Makers-Oakland-University/laser-tanks/Image Recognition/ABS-or-PLA Big.jpg

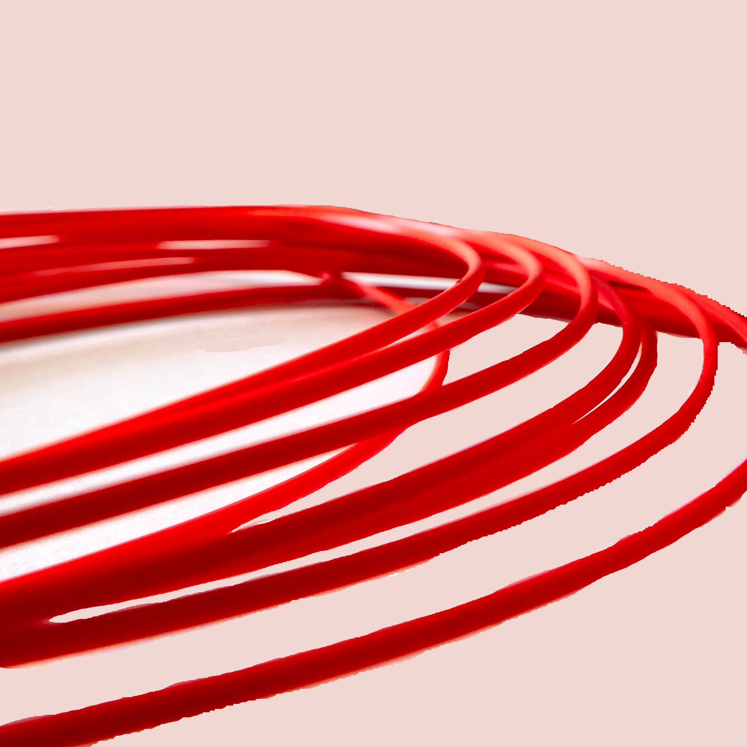
Image Recognition/ABS-or-PLA Big.jpg
