Makers-Oakland-University/laser-tanks/Image Recognition/Test Image Group/input/1.PNG

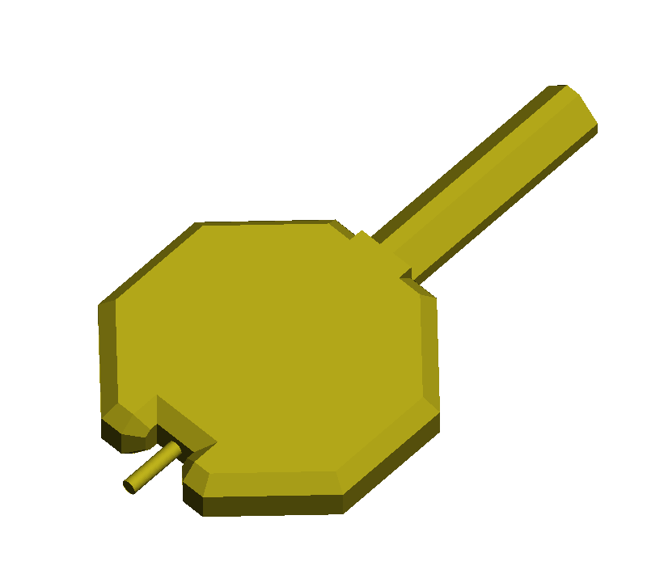
Image Recognition/Test Image Group/input/1.PNG
