Makers-Oakland-University/laser-tanks/Image Recognition/Test Image Group/input/2.PNG

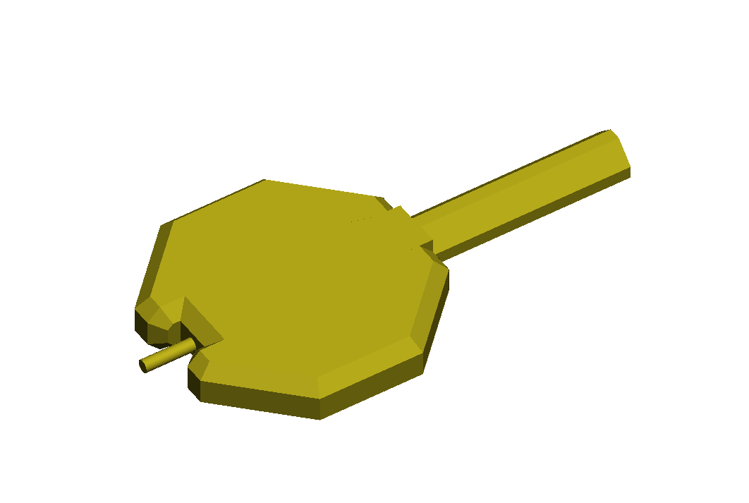
Image Recognition/Test Image Group/input/2.PNG
