Makers-Oakland-University/laser-tanks/Image Recognition/Test Image Group/input/3.PNG

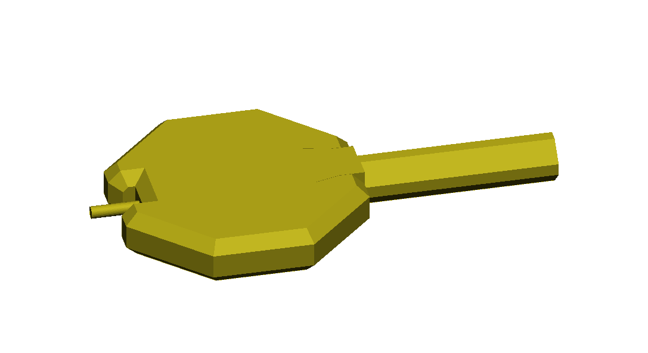
Image Recognition/Test Image Group/input/3.PNG
