Makers-Oakland-University/laser-tanks/Image Recognition/Test Image Group/input/4.PNG

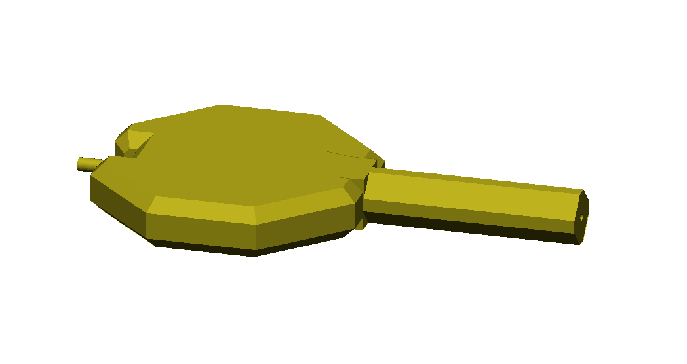
Image Recognition/Test Image Group/input/4.PNG
