Makers-Oakland-University/laser-tanks/Image Recognition/Test Image Group/input/5.PNG

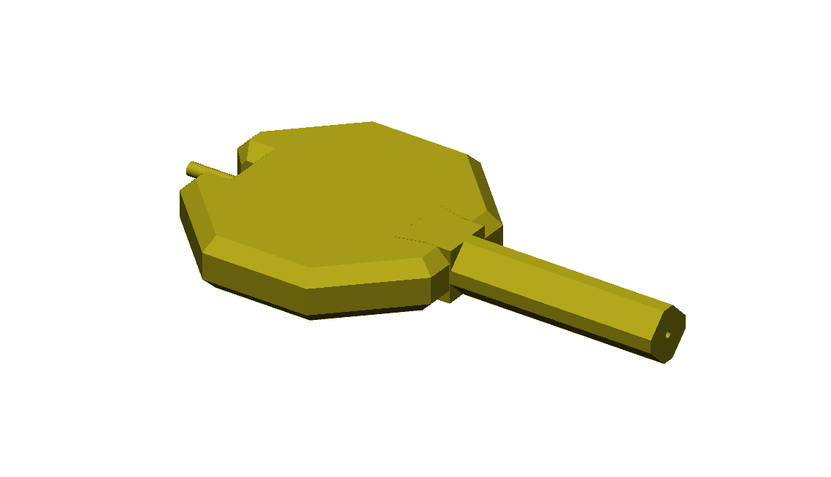
Image Recognition/Test Image Group/input/5.PNG
