Makers-Oakland-University/laser-tanks/Image Recognition/Test Image Group/input/6.PNG

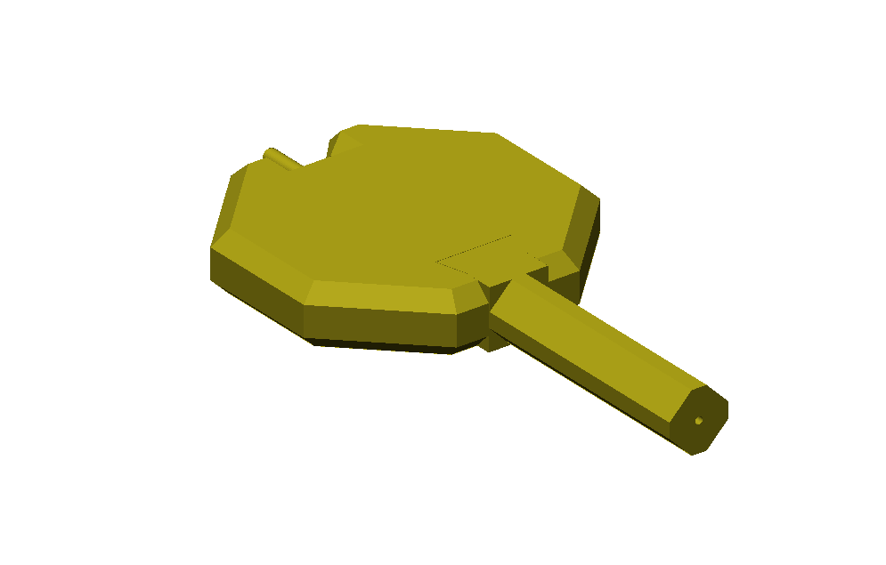
Image Recognition/Test Image Group/input/6.PNG
