Makers-Oakland-University/laser-tanks/Image Recognition/Test Image Group/input/7.PNG

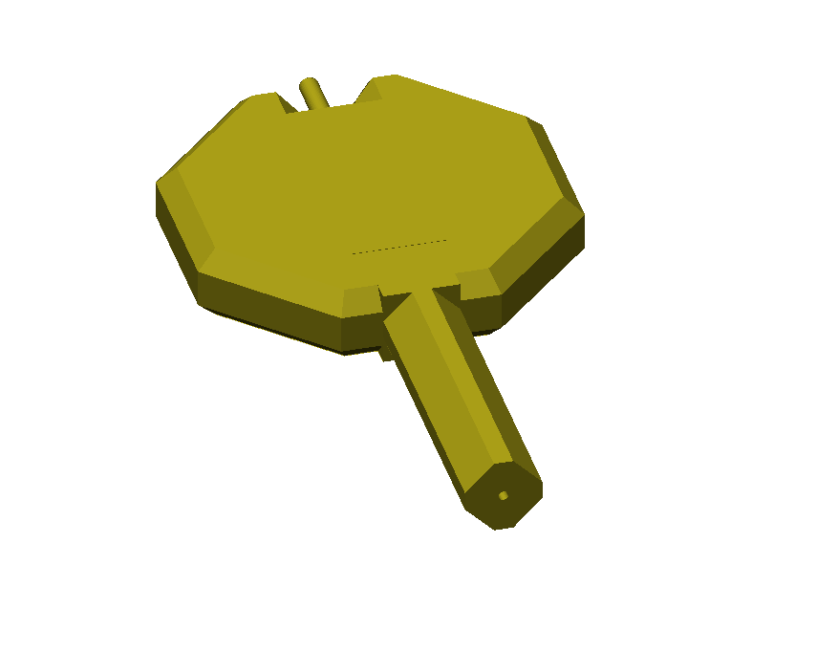
Image Recognition/Test Image Group/input/7.PNG
