Makers-Oakland-University/laser-tanks/Image Recognition/Test Image Group/input/8.PNG

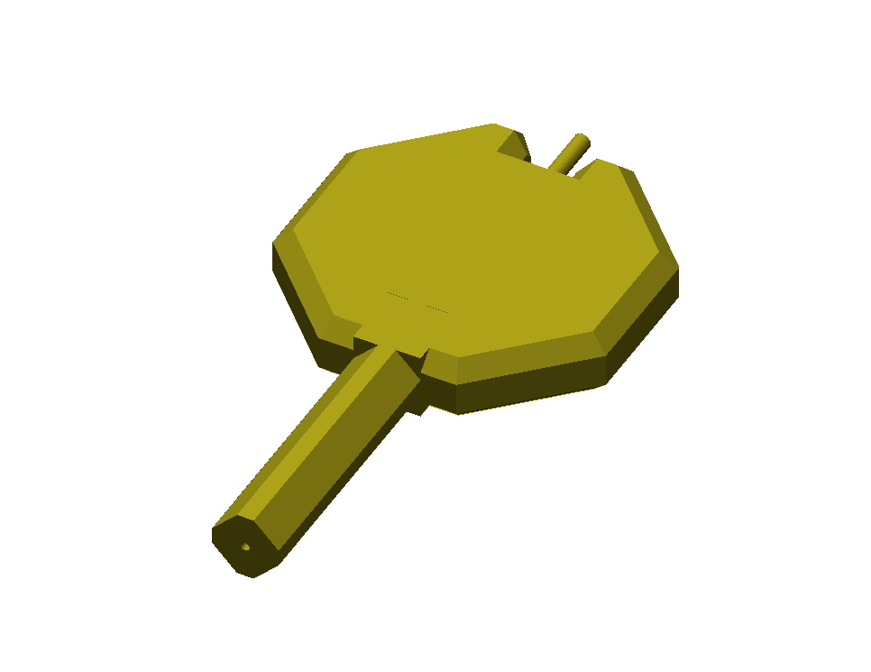
Image Recognition/Test Image Group/input/8.PNG
