Makers-Oakland-University/laser-tanks/Image Recognition/Test Image Group/input/9.PNG

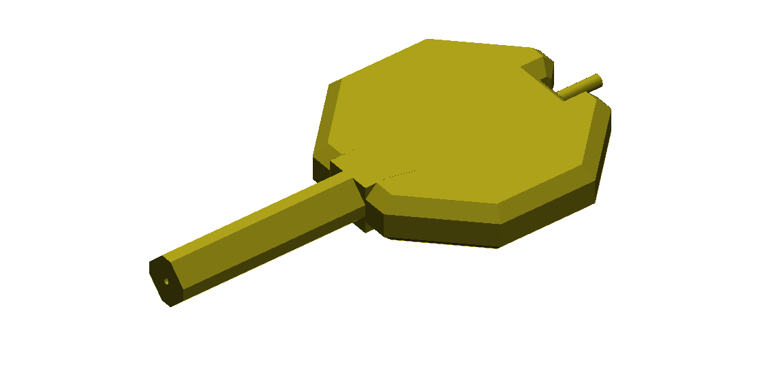
Image Recognition/Test Image Group/input/9.PNG
