Makers-Oakland-University/laser-tanks/Image Recognition/Test Image Group/input/10.PNG

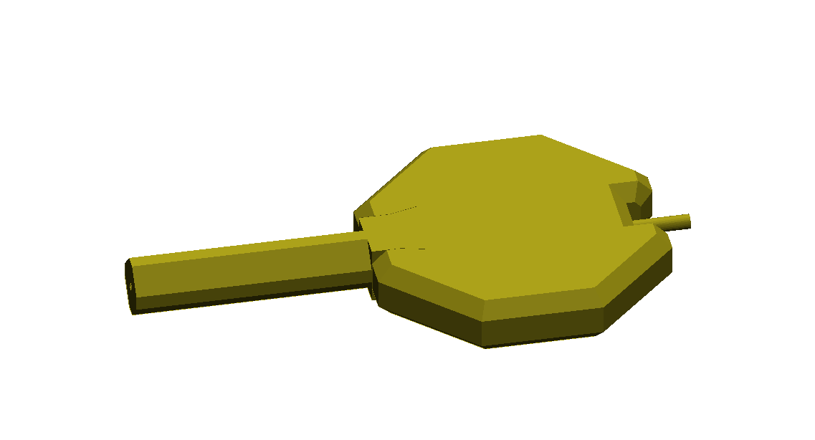
Image Recognition/Test Image Group/input/10.PNG
