Makers-Oakland-University/laser-tanks/Image Recognition/Test Image Group/input/11.PNG

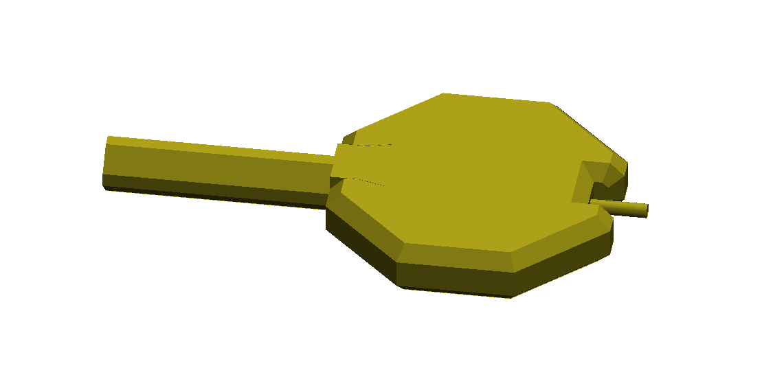
Image Recognition/Test Image Group/input/11.PNG
