Makers-Oakland-University/laser-tanks/Image Recognition/Test Image Group/input/12.PNG

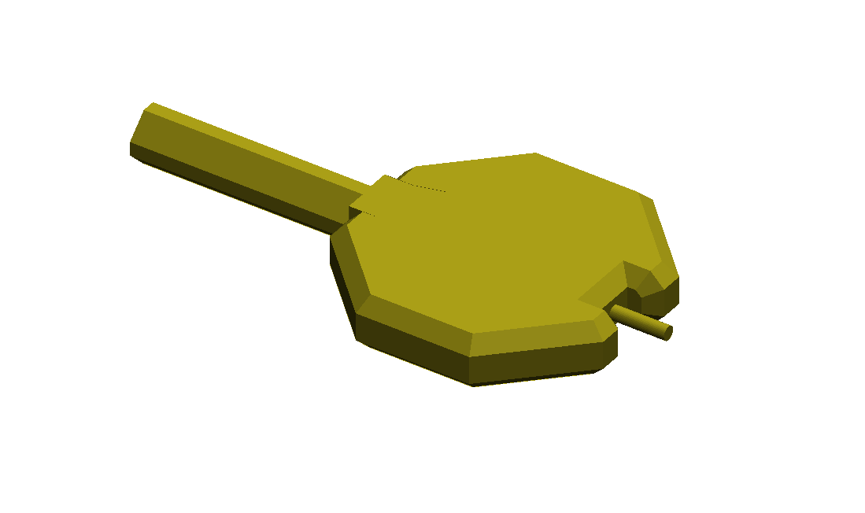
Image Recognition/Test Image Group/input/12.PNG
