Makers-Oakland-University/laser-tanks/Image Recognition/Test Image Group/input/13.PNG

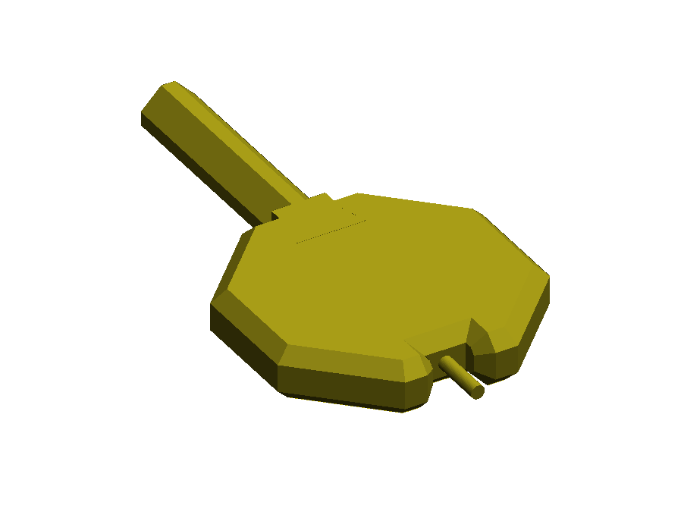
Image Recognition/Test Image Group/input/13.PNG
