Makers-Oakland-University/laser-tanks/Image Recognition/Test Image Group/input/side view.PNG

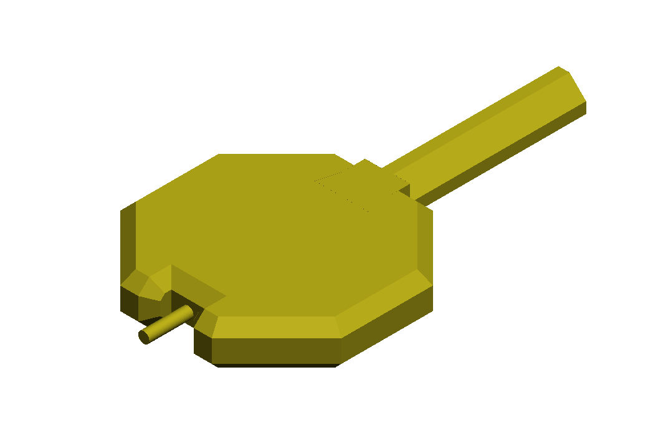
Image Recognition/Test Image Group/input/side view.PNG
