Makers-Oakland-University/laser-tanks/laser_tanks_r2/laser_tanks_r2/laser_tanks_r2.sch

## KiCad design laser_tanks_r2/laser_tanks_r2/laser_tanks_r2.sch (2020-03-07)

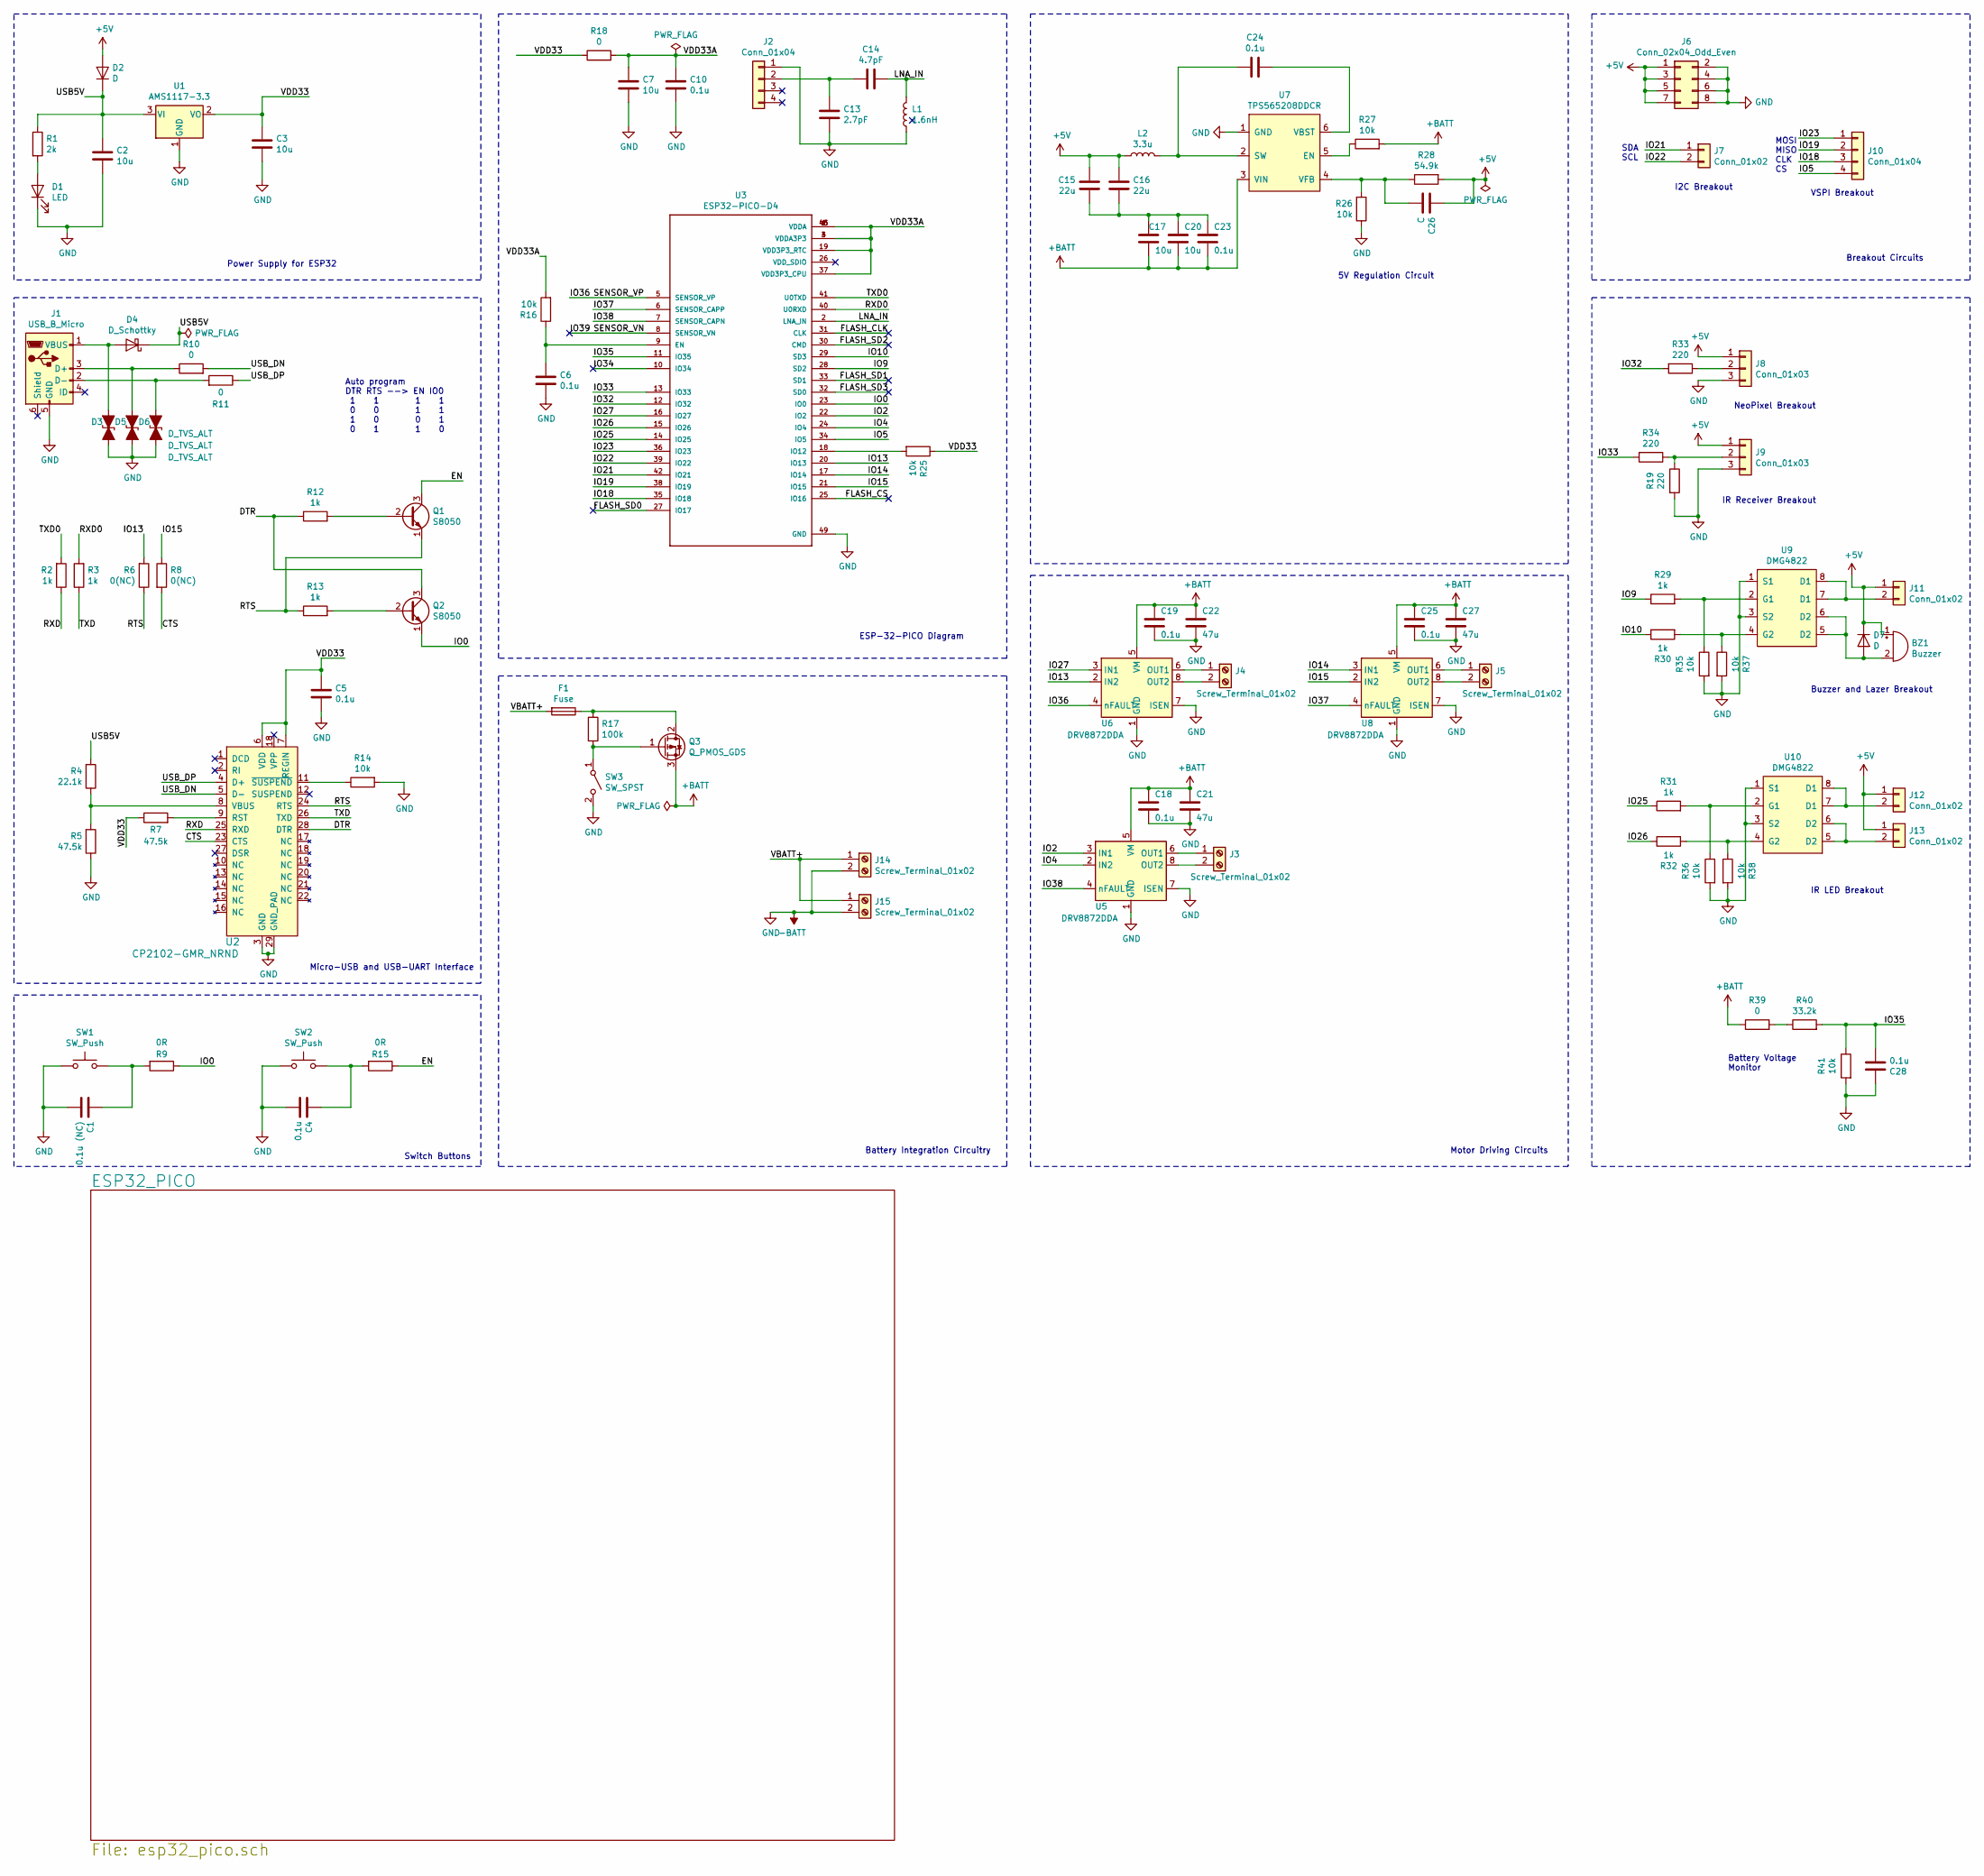
[picture p21: schematic laser_tanks_r2.sch]

Parts:
BZ1: Buzzer; Piezo_Transducer_THT_PS1240P02BT
C1: 0.1u (NC); C_0603_1608Metric_Pad1.05x0.95mm_HandSolder
C2, C3, C7, C17, C20: 10u; C_0805_2012Metric_Pad1.15x1.40mm_HandSolder
C4, C5, C6, C10, C18, C19, C23, C24, C25, C28: 0.1u; C_0603_1608Metric_Pad1.05x0.95mm_HandSolder
C13: 2.7pF; C_0603_1608Metric_Pad1.05x0.95mm_HandSolder
C14: 4.7pF; C_0603_1608Metric_Pad1.05x0.95mm_HandSolder
C15, C16: 22u; C_1206_3216Metric_Pad1.42x1.75mm_HandSolder
C21, C22, C27: 47u; CP_Elec_6.3x5.4
C26: C; C_0805_2012Metric_Pad1.15x1.40mm_HandSolder
D1: LED
D2, D7: D
D3, D5, D6: D_TVS_ALT
D4: D_Schottky
F1: Fuse
J1: USB_B_Micro
J2, J10: Conn_01x04
J3, J4, J5, J14, J15: Screw_Terminal_01x02
J6: Conn_02x04_Odd_Even
J7, J11, J12, J13: Conn_01x02
J8, J9: Conn_01x03
L1: 1.6nH
L2: 3.3u
Q1, Q2: S8050; TO-92_Inline
Q3: Q_PMOS_GDS
R1: 2k
R2, R3, R12, R13, R29, R30, R31, R32: 1k
R4: 22.1k
R5, R7: 47.5k
R6, R8: 0(NC)
R9, R15: 0R
R10, R11, R18, R39: 0
R14, R16, R25, R26, R27, R35, R36, R37, R38, R41: 10k
R17: 100k
R19, R33, R34: 220
R28: 54.9k
R40: 33.2k
SW1, SW2: SW_Push
SW3: SW_SPST
U1: AMS1117-3.3; SOT-223-3_TabPin2
U2: CP2102-GMR_NRND; VFQFN-28-1EP_5x5mm; MPN CP2102-GMR; Digi-Key_PN 336-1160-1-ND
U3: ESP32-PICO-D4; PQFN50P700X700X104-49N
U5, U6, U8: DRV8872DDA; Texas_HTSOP-8-1EP_3.9x4.9mm_P1.27mm_EP2.95x4.9mm_Mask2.4x3.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
U7: TPS565208DDCR
U9, U10: DMG4822

Connections:
+5V: BZ1.1 (-), C15.2, C16.2, C26.1, D2.2 (A), D7.1 (K), J6.1, J6.3, J6.5, J6.7, J8.1, J9.1, J11.1, J12.1, J13.1, L2.1, R28.2
+BATT: C17.1, C18.1, C19.1, C20.2, C21.1, C22.1, C23.2, C25.1, C27.1, Q3.3 (S), R27.2, R39.1, U5.5 (VM), U6.5 (VM), U7.3 (VIN), U8.5 (VM)
-BATT: C1.2, C2.2, C3.2, C4.2, C5.2, C6.2, C7.2, C10.2, C13.2, C18.2, C19.2, C21.2, C22.2, C25.2, C27.2, C28.1, D1.1 (K), D3.2 (A2), D5.2 (A2), D6.2 (A2), J1.5 (GND), J2.1, J6.2, J6.4, J6.6, J6.8, J8.3, J9.3, J14.2, J15.2, L1.1, R5.1, R14.2, R19.2, R26.1, R35.2, R36.2, R37.2, R38.2, R41.2, SW1.1, SW2.1, SW3.2 (B), U1.1 (GND), U2.3 (GND), U2.29 (GND_PAD), U3.49 (GND), U5.1 (GND), U5.7 (ISEN), U5.9 (GND), U6.1 (GND), U6.7 (ISEN), U6.9 (GND), U7.1 (GND), U8.1 (GND), U8.7 (ISEN), U8.9 (GND), U9.1 (S1), U9.3 (S2), U10.1 (S1), U10.3 (S2)
CTS: R8.2, U2.23 (CTS)
DTR: Q2.3 (C), R12.1, U2.28 (DTR)
EN: Q1.3 (C), R15.1
FLASH_CLK: U3.31 (CLK)
FLASH_CS: U3.25 (IO16)
FLASH_SD0: U3.27 (IO17)
FLASH_SD1: U3.33 (SD1)
FLASH_SD2: U3.30 (CMD)
FLASH_SD3: U3.32 (SD0)
IO0: Q2.1 (E), R9.1, U3.23 (IO0)
IO2: U3.22 (IO2), U5.3 (IN1)
IO4: U3.24 (IO4), U5.2 (IN2)
IO5: J10.4, U3.34 (IO5)
IO9: R29.1, U3.28 (SD2)
IO10: R30.1, U3.29 (SD3)
IO13: R6.2, U3.20 (IO13), U6.2 (IN2)
IO14: U3.17 (IO14), U8.3 (IN1)
IO15: R8.1, U3.21 (IO15), U8.2 (IN2)
IO18: J10.3, U3.35 (IO18)
IO19: J10.2, U3.38 (IO19)
IO21: J7.1, U3.42 (IO21)
IO22: J7.2, U3.39 (IO22)
IO23: J10.1, U3.36 (IO23)
IO25: R31.1, U3.14 (IO25)
IO26: R32.1, U3.15 (IO26)
IO27: U3.16 (IO27), U6.3 (IN1)
IO32: R33.2, U3.12 (IO32)
IO33: R34.2, U3.13 (IO33)
IO34: U3.10 (IO34)
IO35: C28.2, R40.2, R41.1, U3.11 (IO35)
IO36: U3.5 (SENSOR_VP), U6.4 (nFAULT)
IO37: U3.6 (SENSOR_CAPP), U8.4 (nFAULT)
IO38: U3.7 (SENSOR_CAPN), U5.4 (nFAULT)
IO39: U3.8 (SENSOR_VN)
LNA_IN: C14.1, L1.2, U3.2 (LNA_IN)
unnamed: BZ1.2 (+), D7.2 (A), U9.5 (D2), U9.6 (D2)
unnamed: C1.1, R9.2, SW1.2
unnamed: C4.1, R15.2, SW2.2
unnamed: C6.1, R16.1, U3.9 (EN)
unnamed: C13.1, C14.2, J2.2
unnamed: C15.1, C16.1, C17.2, C20.1, C23.1
unnamed: C24.1, U7.6 (VBST)
unnamed: C24.2, L2.2, U7.2 (SW)
unnamed: C26.2, R26.2, R28.1, U7.4 (VFB)
unnamed: D1.2 (A), R1.2
unnamed: D3.1 (A1), D4.2 (A), J1.1 (VBUS)
unnamed: D5.1 (A1), J1.3 (D+), R10.1
unnamed: D6.1 (A1), J1.2 (D-), R11.2
unnamed: F1.1, Q3.2 (D), R17.1
unnamed: J3.1, U5.6 (OUT1)
unnamed: J3.2, U5.8 (OUT2)
unnamed: J4.1, U6.6 (OUT1)
unnamed: J4.2, U6.8 (OUT2)
unnamed: J5.1, U8.6 (OUT1)
unnamed: J5.2, U8.8 (OUT2)
unnamed: J8.2, R33.1
unnamed: J9.2, R19.1, R34.1
unnamed: J11.2, U9.7 (D1), U9.8 (D1)
unnamed: J12.2, U10.7 (D1), U10.8 (D1)
unnamed: J13.2, U10.5 (D2), U10.6 (D2)
unnamed: Q1.2 (B), R12.2
unnamed: Q2.2 (B), R13.2
unnamed: Q3.1 (G), R17.2, SW3.1 (A)
unnamed: R4.1, R5.2, U2.8 (VBUS)
unnamed: R7.2, U2.9 (RST)
unnamed: R14.1, U2.11 (~SUSPEND)
unnamed: R25.2, U3.18 (IO12)
unnamed: R27.1, U7.5 (EN)
unnamed: R29.2, R35.1, U9.2 (G1)
unnamed: R30.2, R37.1, U9.4 (G2)
unnamed: R31.2, R36.1, U10.2 (G1)
unnamed: R32.2, R38.1, U10.4 (G2)
unnamed: R39.2, R40.1
RTS: Q1.1 (E), R6.1, R13.1, U2.24 (RTS)
RXD: R2.1, U2.25 (RXD)
RXD0: R3.2, U3.40 (U0RXD)
TXD: R3.1, U2.26 (TXD)
TXD0: R2.2, U3.41 (U0TXD)
USB5V: C2.1, D2.1 (K), D4.1 (K), R1.1, R4.2, U1.3 (VI)
USB_DN: R10.2, U2.5 (D-)
USB_DP: R11.1, U2.4 (D+)
VBATT+: F1.2, J14.1, J15.1
VDD33: C3.1, C5.1, R7.1, R18.1, R25.1, U1.2 (VO), U2.6 (VDD), U2.7 (REGIN)
VDD33A: C7.1, C10.1, R16.2, R18.2, U3.1 (VDDA), U3.3 (VDDA3P3), U3.4 (VDDA3P3), U3.19 (VDD3P3_RTC), U3.37 (VDD3P3_CPU), U3.43 (VDDA), U3.46 (VDDA)

Notes on the sheet:
Power Supply for ESP32
Auto program DTR RTS --> EN IO0 1 1 1 1 0 0 1 1 1 0 0 1 0 1 1 0
Micro-USB and USB-UART Interface
Switch Buttons
ESP-32-PICO Diagram
5V Regulation Circuit
VSPI Breakout
MOSI MISO CLK CS
I2C Breakout
SDA SCL
Battery Voltage Monitor
Motor Driving Circuits
Breakout Circuits
IR Receiver Breakout
Buzzer and Lazer Breakout
IR LED Breakout
NeoPixel Breakout
Battery Integration Circuitry
