Makers-Oakland-University/laser-tanks/laser_tanks_r2/laser_tanks_r2/laser_tanks_r3.sch

## KiCad design laser_tanks_r2/laser_tanks_r2/laser_tanks_r3.sch (2020-03-07)

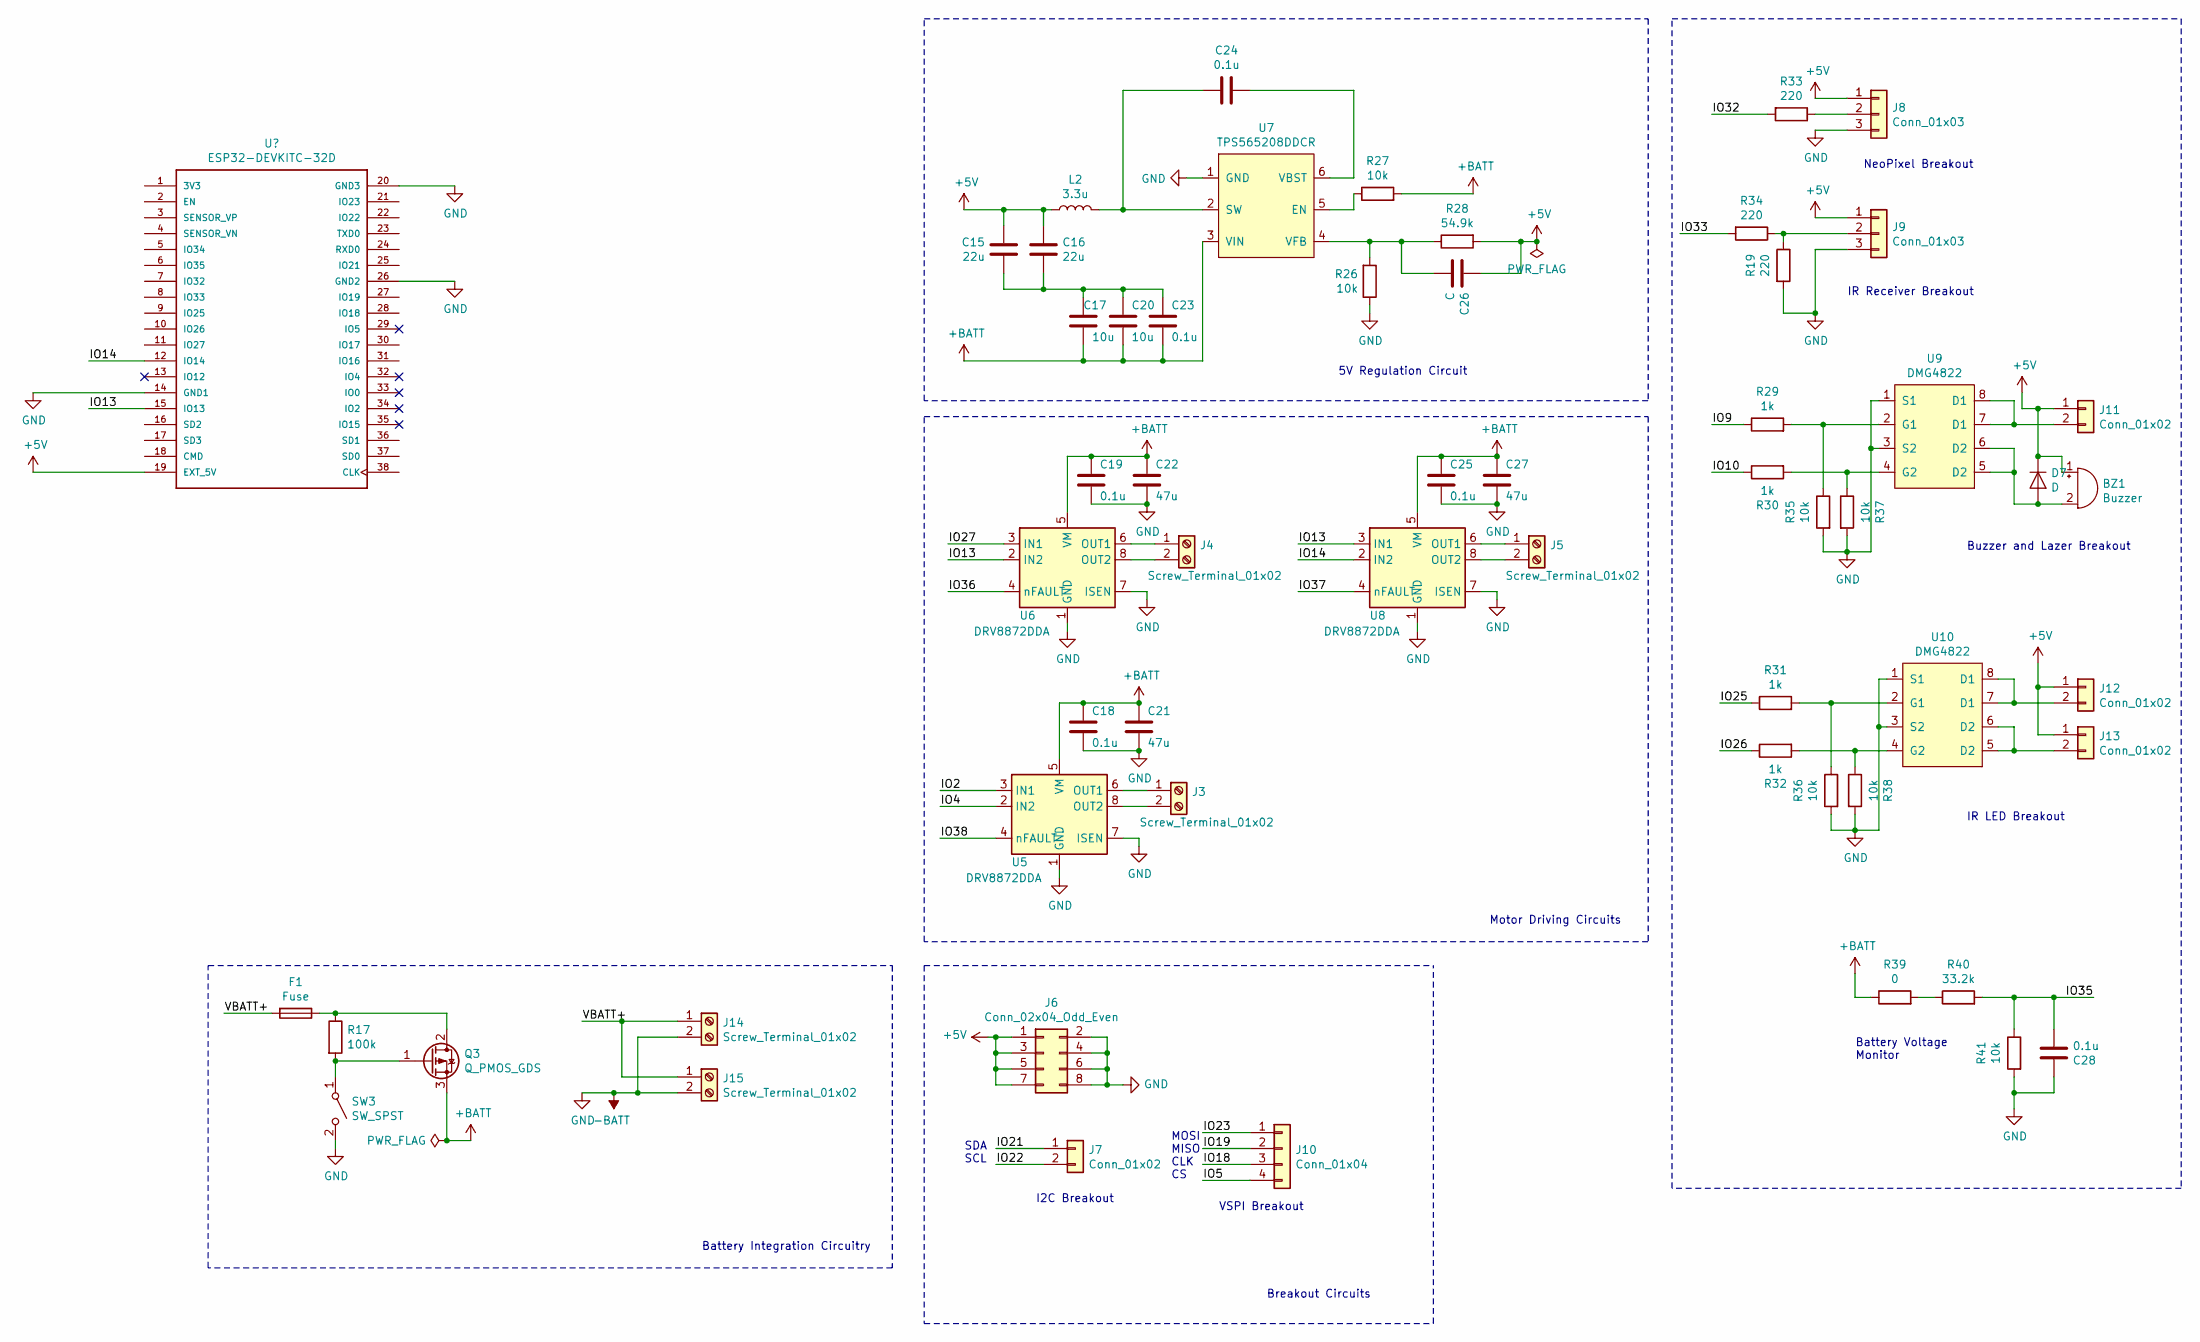
[picture p22: schematic laser_tanks_r3.sch]

Parts:
BZ1: Buzzer; Piezo_Transducer_THT_PS1240P02BT
C15, C16: 22u; C_1206_3216Metric_Pad1.42x1.75mm_HandSolder
C17, C20: 10u; C_0805_2012Metric_Pad1.15x1.40mm_HandSolder
C18, C19, C23, C24, C25, C28: 0.1u; C_0603_1608Metric_Pad1.05x0.95mm_HandSolder
C21, C22, C27: 47u; CP_Elec_6.3x5.4
C26: C; C_0805_2012Metric_Pad1.15x1.40mm_HandSolder
D7: D
F1: Fuse
J3, J4, J5, J14, J15: Screw_Terminal_01x02
J6: Conn_02x04_Odd_Even
J7, J11, J12, J13: Conn_01x02
J8, J9: Conn_01x03
J10: Conn_01x04
L2: 3.3u
Q3: Q_PMOS_GDS
R17: 100k
R19, R33, R34: 220
R26, R27, R35, R36, R37, R38, R41: 10k
R28: 54.9k
R29, R30, R31, R32: 1k
R39: 0
R40: 33.2k
SW3: SW_SPST
U5, U6, U8: DRV8872DDA; Texas_HTSOP-8-1EP_3.9x4.9mm_P1.27mm_EP2.95x4.9mm_Mask2.4x3.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
U7: TPS565208DDCR
U9, U10: DMG4822

Connections:
+5V: BZ1.1 (-), C15.2, C16.2, C26.1, D7.1 (K), J6.1, J6.3, J6.5, J6.7, J8.1, J9.1, J11.1, J12.1, J13.1, L2.1, R28.2
+BATT: C17.1, C18.1, C19.1, C20.2, C21.1, C22.1, C23.2, C25.1, C27.1, Q3.3 (S), R27.2, R39.1, U5.5 (VM), U6.5 (VM), U7.3 (VIN), U8.5 (VM)
-BATT: C18.2, C19.2, C21.2, C22.2, C25.2, C27.2, C28.1, J6.2, J6.4, J6.6, J6.8, J8.3, J9.3, J14.2, J15.2, R19.2, R26.1, R35.2, R36.2, R37.2, R38.2, R41.2, SW3.2 (B), U5.1 (GND), U5.7 (ISEN), U5.9 (GND), U6.1 (GND), U6.7 (ISEN), U6.9 (GND), U7.1 (GND), U8.1 (GND), U8.7 (ISEN), U8.9 (GND), U9.1 (S1), U9.3 (S2), U10.1 (S1), U10.3 (S2)
IO2: U5.3 (IN1)
IO4: U5.2 (IN2)
IO5: J10.4
IO9: R29.1
IO10: R30.1
IO13: U6.2 (IN2), U8.3 (IN1)
IO14: U8.2 (IN2)
IO18: J10.3
IO19: J10.2
IO21: J7.1
IO22: J7.2
IO23: J10.1
IO25: R31.1
IO26: R32.1
IO27: U6.3 (IN1)
IO32: R33.2
IO33: R34.2
IO35: C28.2, R40.2, R41.1
IO36: U6.4 (nFAULT)
IO37: U8.4 (nFAULT)
IO38: U5.4 (nFAULT)
unnamed: BZ1.2 (+), D7.2 (A), U9.5 (D2), U9.6 (D2)
unnamed: C15.1, C16.1, C17.2, C20.1, C23.1
unnamed: C24.1, U7.6 (VBST)
unnamed: C24.2, L2.2, U7.2 (SW)
unnamed: C26.2, R26.2, R28.1, U7.4 (VFB)
unnamed: F1.1, Q3.2 (D), R17.1
unnamed: J3.1, U5.6 (OUT1)
unnamed: J3.2, U5.8 (OUT2)
unnamed: J4.1, U6.6 (OUT1)
unnamed: J4.2, U6.8 (OUT2)
unnamed: J5.1, U8.6 (OUT1)
unnamed: J5.2, U8.8 (OUT2)
unnamed: J8.2, R33.1
unnamed: J9.2, R19.1, R34.1
unnamed: J11.2, U9.7 (D1), U9.8 (D1)
unnamed: J12.2, U10.7 (D1), U10.8 (D1)
unnamed: J13.2, U10.5 (D2), U10.6 (D2)
unnamed: Q3.1 (G), R17.2, SW3.1 (A)
unnamed: R27.1, U7.5 (EN)
unnamed: R29.2, R35.1, U9.2 (G1)
unnamed: R30.2, R37.1, U9.4 (G2)
unnamed: R31.2, R36.1, U10.2 (G1)
unnamed: R32.2, R38.1, U10.4 (G2)
unnamed: R39.2, R40.1
VBATT+: F1.2, J14.1, J15.1

Notes on the sheet:
5V Regulation Circuit
VSPI Breakout
MOSI MISO CLK CS
I2C Breakout
SDA SCL
Battery Voltage Monitor
Motor Driving Circuits
Breakout Circuits
IR Receiver Breakout
Buzzer and Lazer Breakout
IR LED Breakout
NeoPixel Breakout
Battery Integration Circuitry
